aepolicht/moboNet/Bulb_Node_PCB/Due/PCB.png

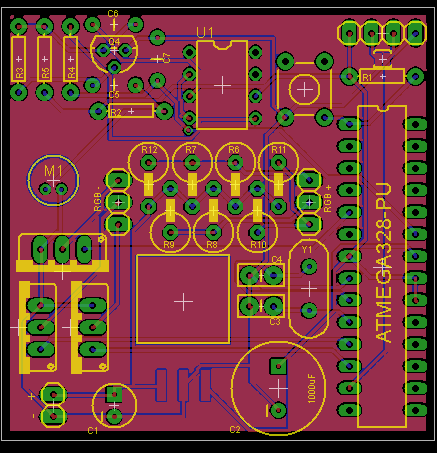
Bulb_Node_PCB/Due/PCB.png
